oshanyalegama/Timer-Based-Aquarium-Light/Enclosure/sketches/Solidworks sketches/Front Sketch.jpg

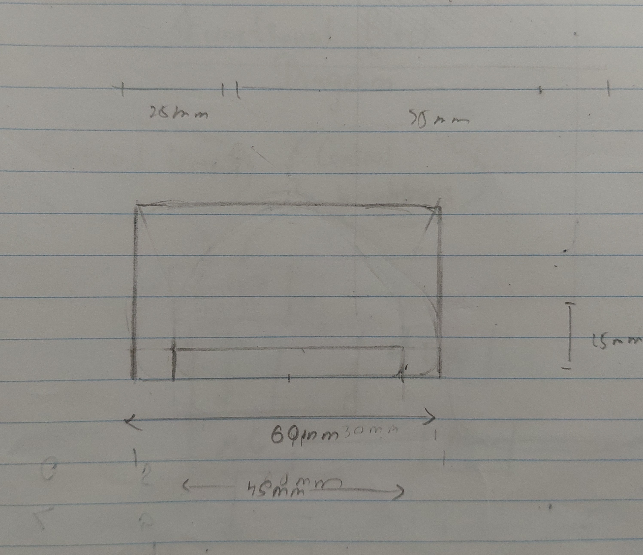
Enclosure/sketches/Solidworks sketches/Front Sketch.jpg
