oshanyalegama/Timer-Based-Aquarium-Light/Enclosure/sketches/Solidworks sketches/Side Sketch copy.jpg

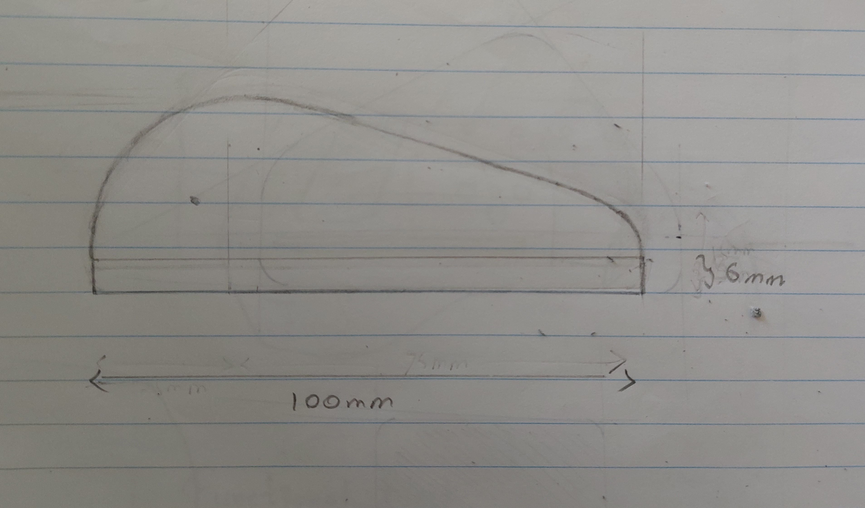
Enclosure/sketches/Solidworks sketches/Side Sketch copy.jpg
