oshanyalegama/Timer-Based-Aquarium-Light/Enclosure/sketches/Solidworks sketches/TOP Sketch.jpg

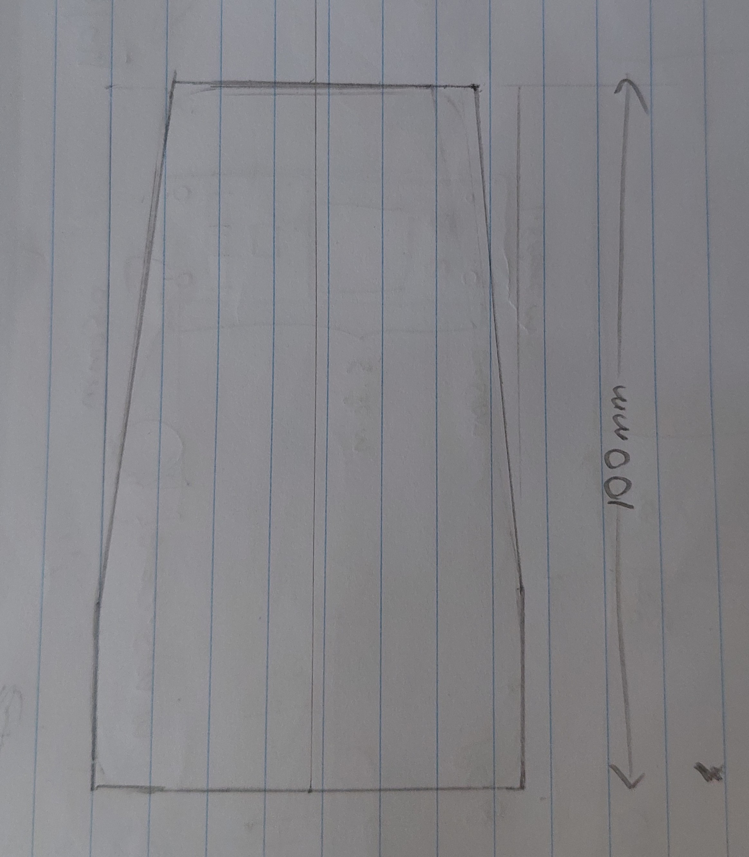
Enclosure/sketches/Solidworks sketches/TOP Sketch.jpg
