oshanyalegama/Timer-Based-Aquarium-Light/Enclosure/sketches/WhatsApp Image 2023-06-08 at 06.24.54.jpeg

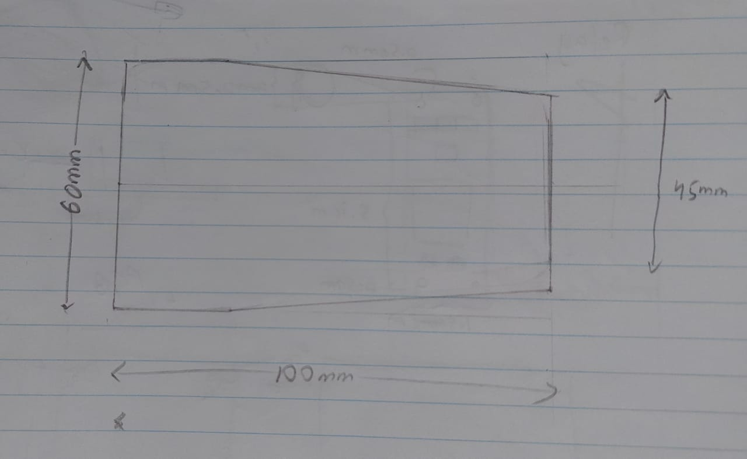
Enclosure/sketches/WhatsApp Image 2023-06-08 at 06.24.54.jpeg
