oshanyalegama/Timer-Based-Aquarium-Light/Enclosure/Final Printed Designs/New folder/Top.STL

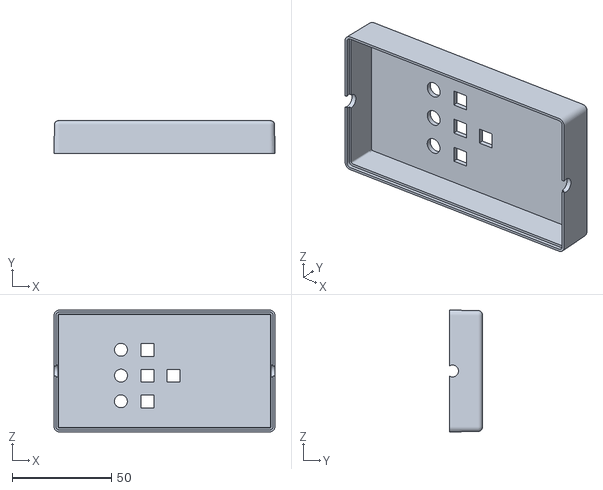
[picture p60: CAD file, 2023-08-28]
Enclosure/Final Printed Designs/New folder/Top.STL
111.4 x 16.5 x 61.4
