oshanyalegama/Timer-Based-Aquarium-Light/Enclosure/Final Printed Designs/past solidworks versioon/top and bottom.SLDPRT

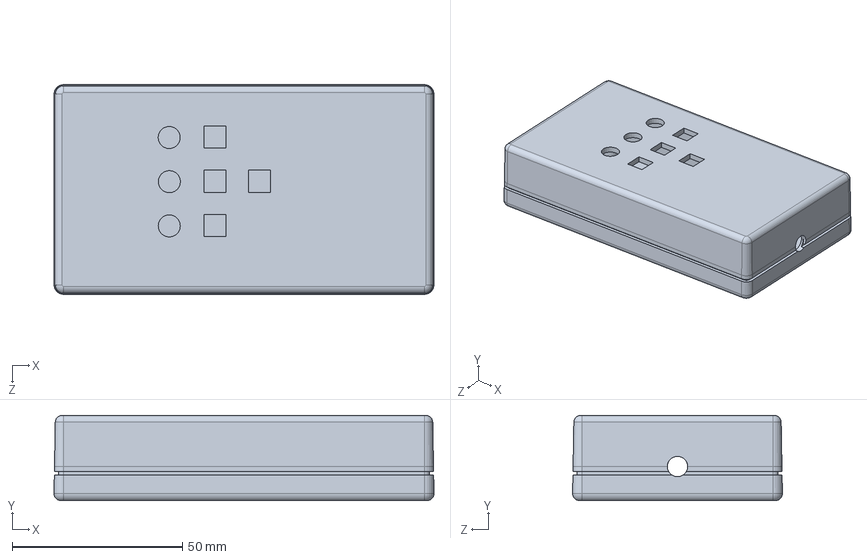
[picture p61: CAD file, 2023-08-28]
Enclosure/Final Printed Designs/past solidworks versioon/top and bottom.SLDPRT
111.7 x 25.0 x 61.7 mm
