oshanyalegama/Timer-Based-Aquarium-Light/Enclosure/Final Printed Designs/second edition/Xyder/final print bottom.STL

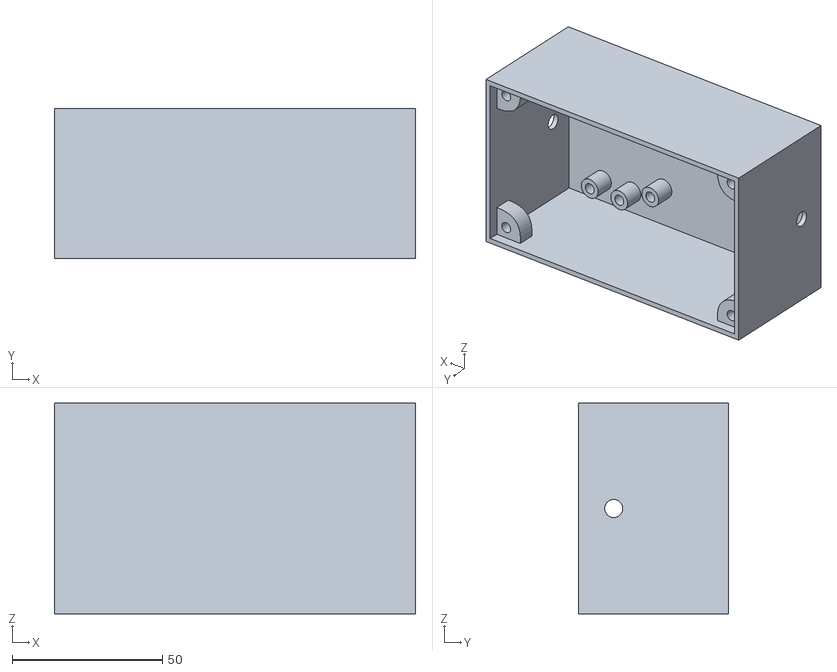
[picture p62: CAD file, 2023-08-28]
Enclosure/Final Printed Designs/second edition/Xyder/final print bottom.STL
120.0 x 50.0 x 70.0
