oshanyalegama/Timer-Based-Aquarium-Light/Enclosure/Initial Design/Solidworks/Relay.stp

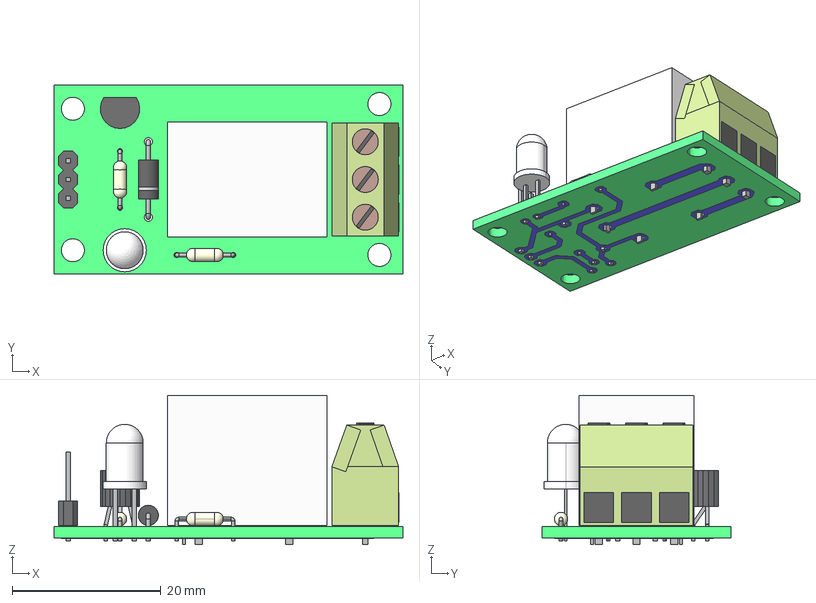
[picture p63: CAD file, 2023-08-28]
Enclosure/Initial Design/Solidworks/Relay.stp
47.0 x 25.4 x 20.1 mm
