oshanyalegama/Timer-Based-Aquarium-Light/Enclosure/Final Printed Designs/past solidworks versioon/Body1.SLDPRT

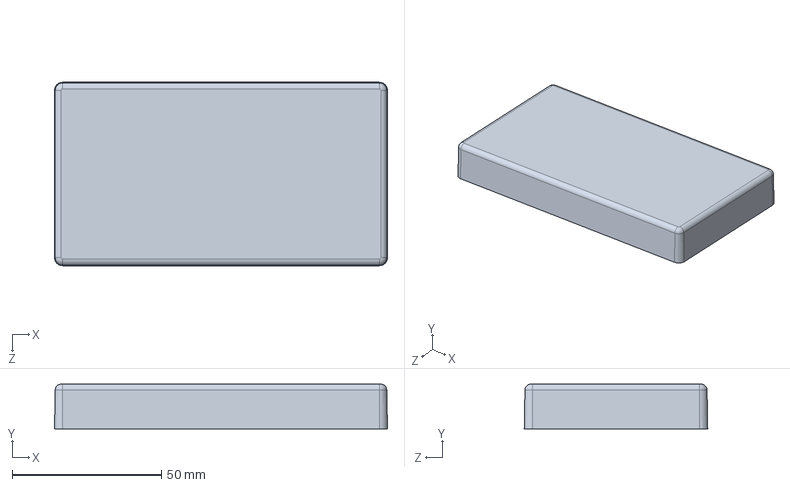
[picture p64: CAD file, 2023-08-28]
Enclosure/Final Printed Designs/past solidworks versioon/Body1.SLDPRT
111.4 x 15.0 x 61.4 mm
