oshanyalegama/Timer-Based-Aquarium-Light/Enclosure/Initial Design/Solidworks/Box.SLDPRT

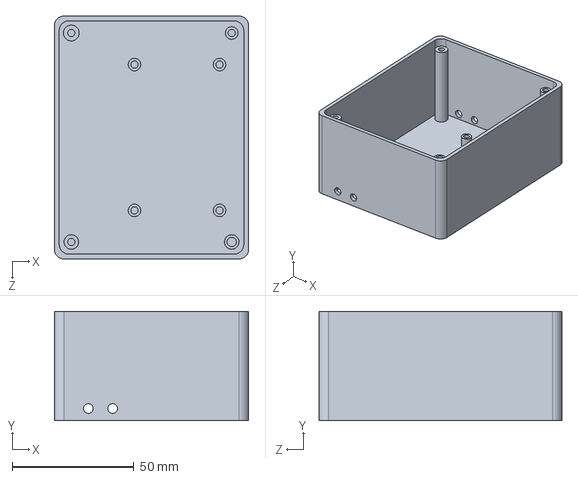
[picture p65: CAD file, 2023-08-28]
Enclosure/Initial Design/Solidworks/Box.SLDPRT
80.0 x 45.0 x 100.0 mm
