oshanyalegama/Timer-Based-Aquarium-Light/Enclosure/Initial Design/Solidworks/Lid.SLDPRT

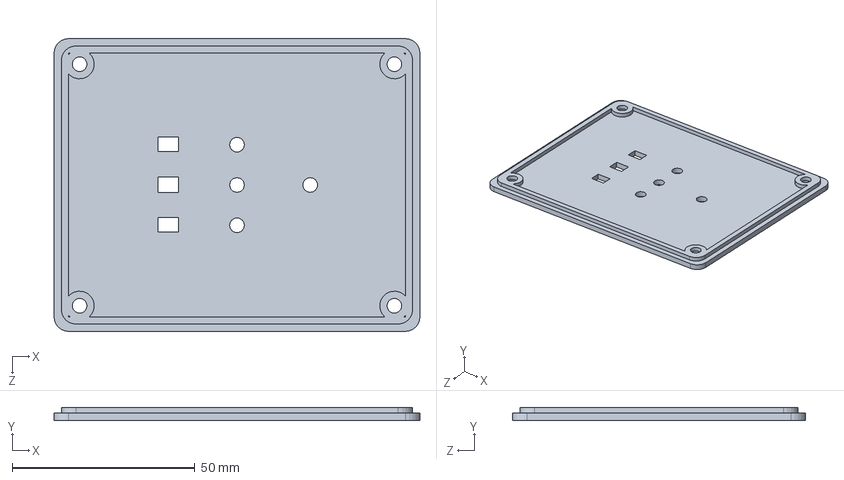
[picture p66: CAD file, 2023-08-28]
Enclosure/Initial Design/Solidworks/Lid.SLDPRT
100.0 x 3.50 x 80.0 mm
