oshanyalegama/Timer-Based-Aquarium-Light/Enclosure/Initial Design/Solidworks/nail.SLDPRT

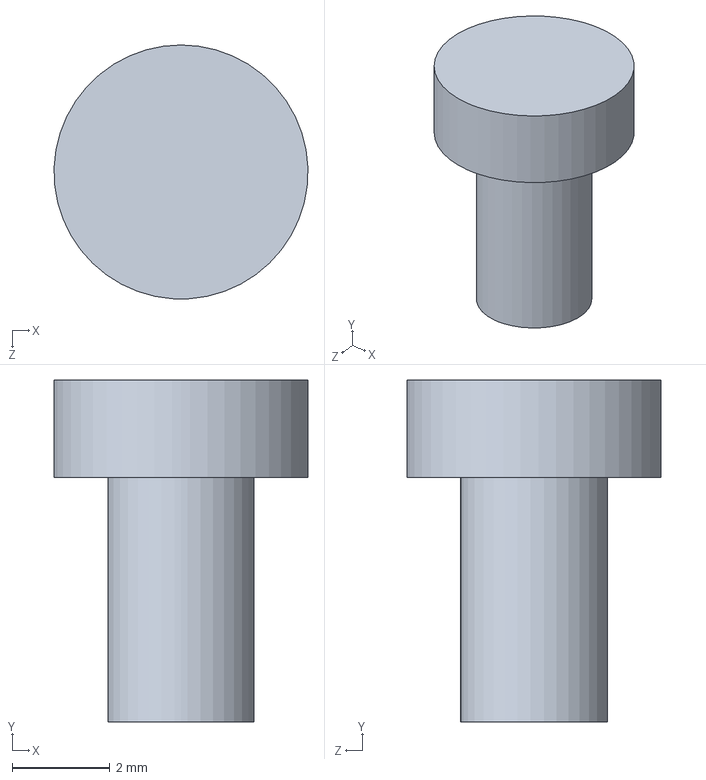
[picture p67: CAD file, 2023-08-28]
Enclosure/Initial Design/Solidworks/nail.SLDPRT
5.20 x 7.00 x 5.20 mm
